requireiot/MyGateway-ESP32-ETH/svn_rev_pre.py

#
# pre-build script to make SVN revision number and platformio env: build type 
# available as a macro for inclusion in version strings etc.
#
# Copyright (C)20204 Bernd Waldmann
#

import subprocess,os,datetime

try:
    revision = (
        subprocess.check_output(["svnversion", "-n", "."])
        .strip()
        .decode("utf-8")
    )
except subprocess.CalledProcessError:
    revision = ""

print("'-DSVN_REV=\"%s\"'" % revision)

Import("env")
pioenv = env['PIOENV']
print("Building ",pioenv)

VERSION_HEADER = 'Revision.h'

HEADER_FILE = """
    // AUTO GENERATED FILE, DO NOT EDIT
    #ifndef SVN_REV
        #define SVN_REV "{}"
    #endif
    #ifndef PIO_ENV
        #define PIO_ENV "{}"
    #endif
    // last checked {}
    """.format(str(revision),str(pioenv),datetime.datetime.now())

if os.environ.get('PLATFORMIO_INCLUDE_DIR') is not None:
    VERSION_HEADER = os.environ.get('PLATFORMIO_INCLUDE_DIR') + os.sep + VERSION_HEADER
elif os.path.exists("include"):
    VERSION_HEADER = "include" + os.sep + VERSION_HEADER
else:
    PROJECT_DIR = env.subst("$PROJECT_DIR")
    os.mkdir(PROJECT_DIR + os.sep + "include")
    VERSION_HEADER = "include" + os.sep + VERSION_HEADER

with open(VERSION_HEADER, 'w+') as FILE:
    FILE.write(HEADER_FILE)
